Peppson/word-clock/faceplate/45x45_example.PNG

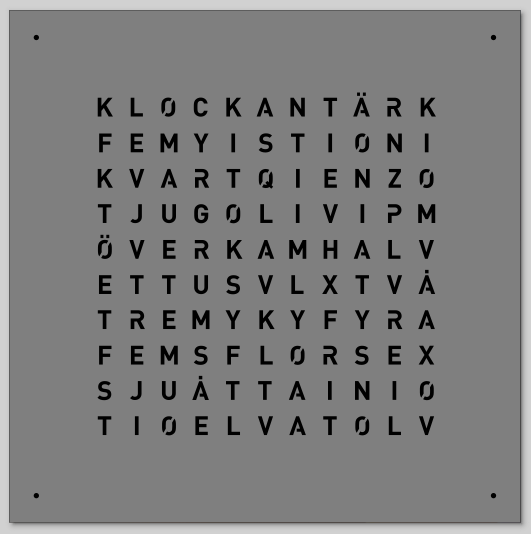
faceplate/45x45_example.PNG
