Peppson/word-clock/images/faceplateTimes.png

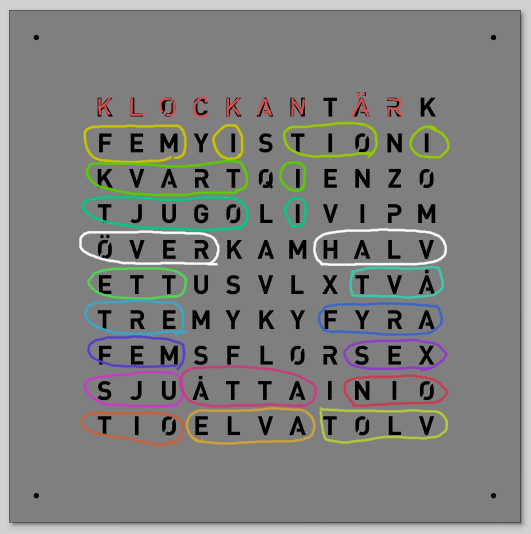
images/faceplateTimes.png
