Peppson/word-clock/images/webPage/Screenshot_1.png

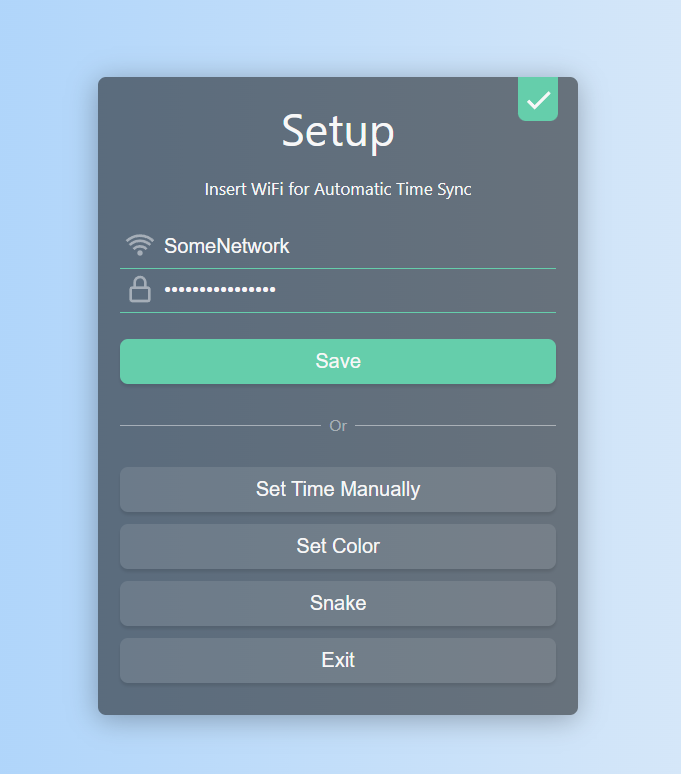
images/webPage/Screenshot_1.png
