Peppson/word-clock/images/webPage/Screenshot_2.png

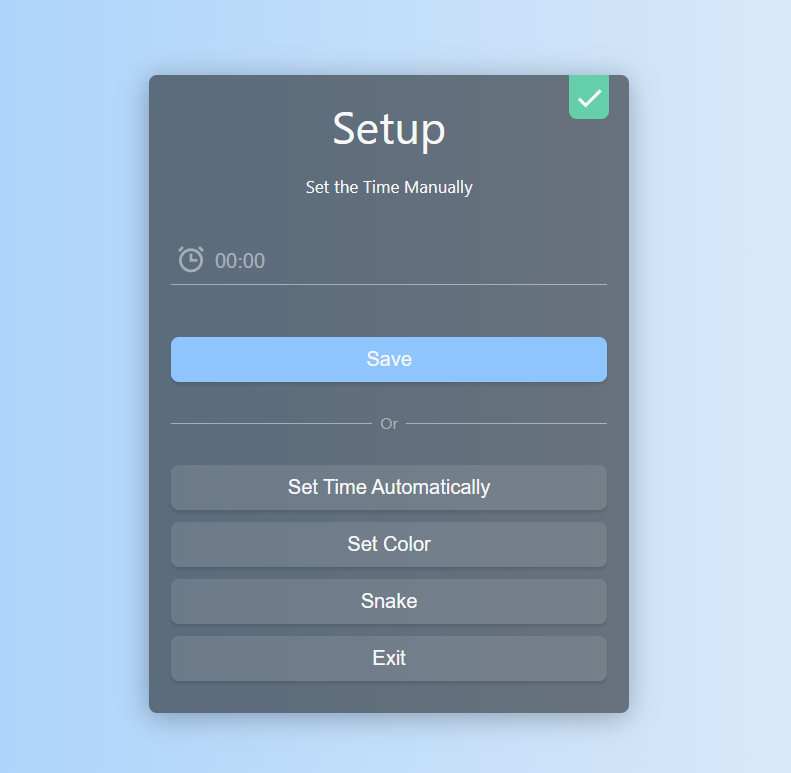
images/webPage/Screenshot_2.png
