Peppson/word-clock/images/webPage/Screenshot_3.png

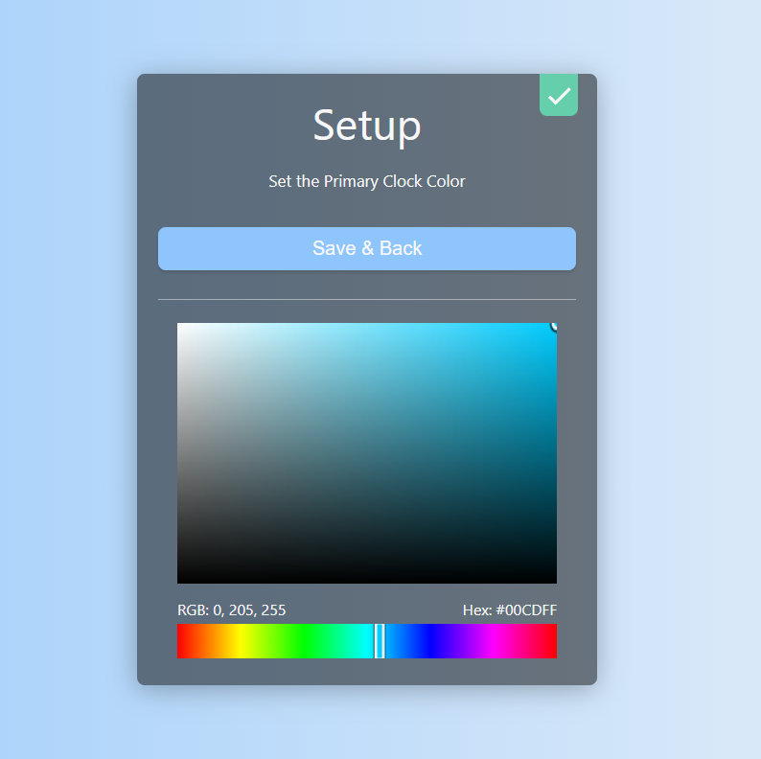
images/webPage/Screenshot_3.png
