Peppson/word-clock/images/webPage/Screenshot_4.png

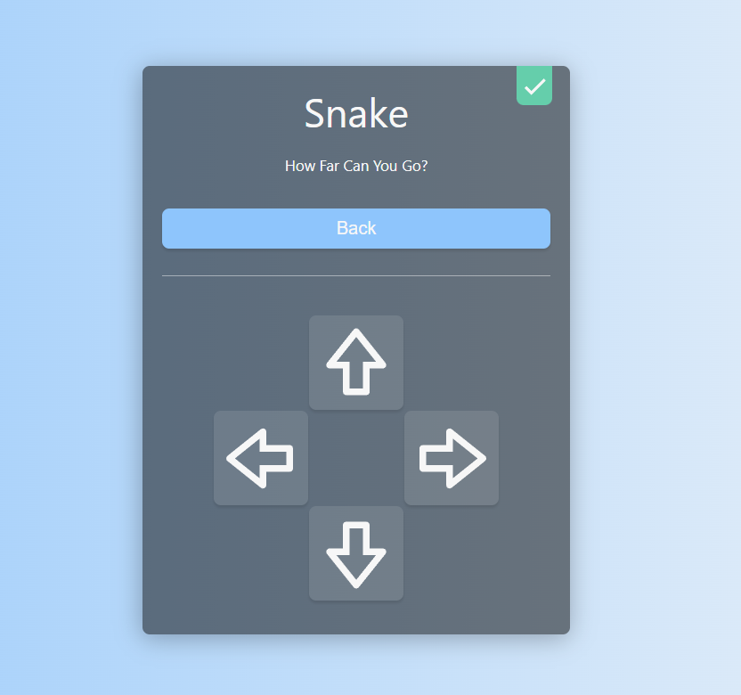
images/webPage/Screenshot_4.png
